Taras-Bilyk/vaz_car/stl_objects/bamper_a.stl

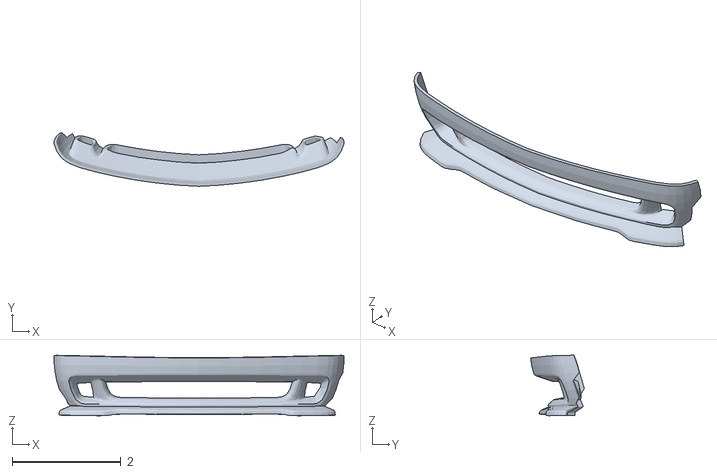
[picture p20: CAD file, 2026-05-01]
stl_objects/bamper_a.stl
5.33 x 0.988 x 1.11
