Taras-Bilyk/vaz_car/stl_objects/splitter_left_bottom.stl

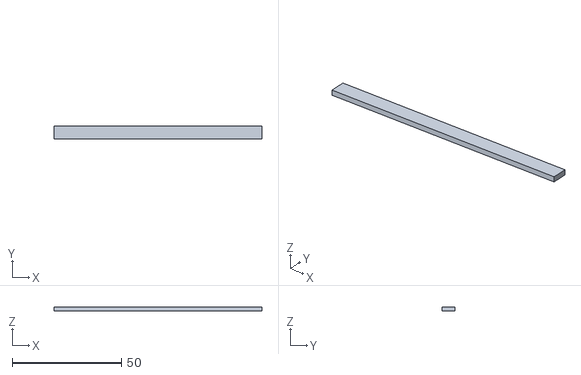
[picture p21: CAD file, 2026-05-01]
stl_objects/splitter_left_bottom.stl
95.0 x 6.00 x 2.00
