Taras-Bilyk/vaz_car/stl_objects/base_bottom.stl

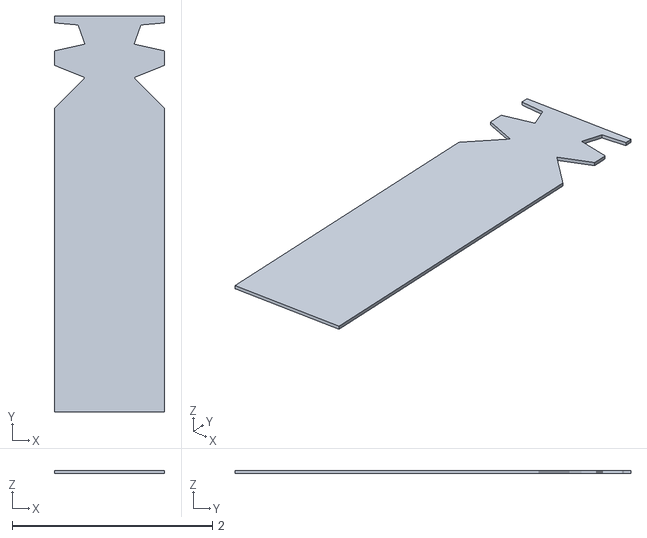
[picture p22: CAD file, 2026-05-01]
stl_objects/base_bottom.stl
1.10 x 3.95 x 0.03
