Taras-Bilyk/vaz_car/stl_objects/kapot.stl

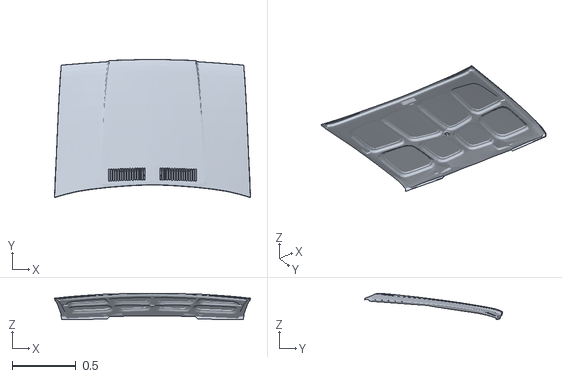
[picture p23: CAD file, 2026-05-01]
stl_objects/kapot.stl
1.54 x 1.09 x 0.208
