Taras-Bilyk/vaz_car/stl_objects/wheel_v2.stl

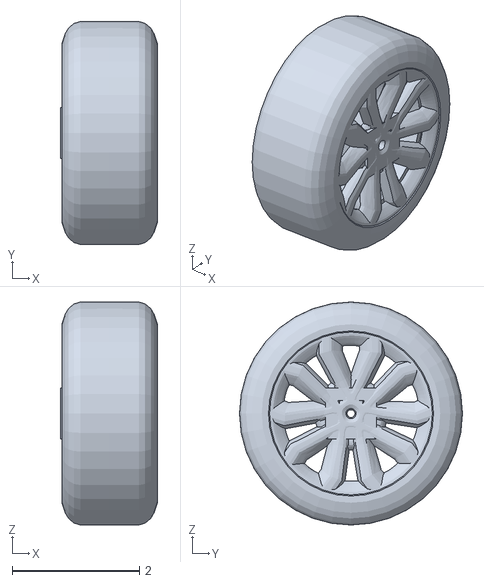
[picture p24: CAD file, 2026-05-01]
stl_objects/wheel_v2.stl
1.52 x 3.50 x 3.50
