Taras-Bilyk/vaz_car/stl_objects/base_body.stl

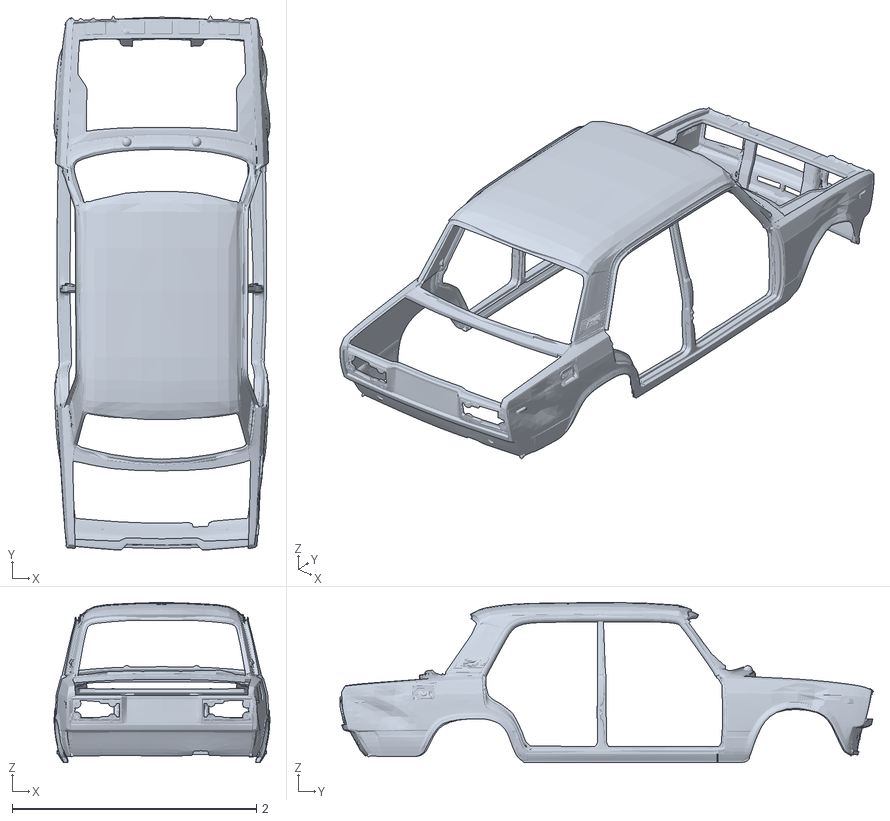
[picture p25: CAD file, 2026-05-01]
stl_objects/base_body.stl
1.77 x 4.38 x 1.31
