Taras-Bilyk/vaz_car/stl_objects/cross_window.stl

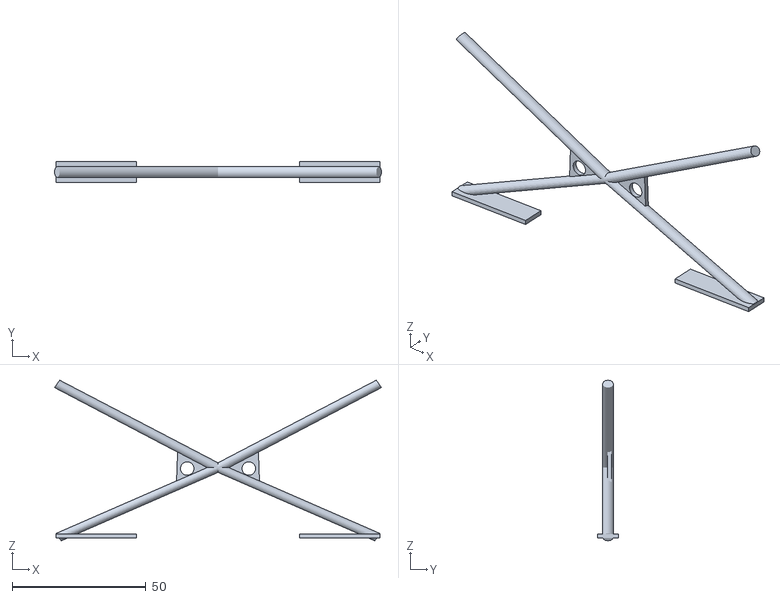
[picture p26: CAD file, 2026-05-01]
stl_objects/cross_window.stl
122.1 x 8.00 x 60.0
