Taras-Bilyk/vaz_car/stl_objects/inc_front.stl

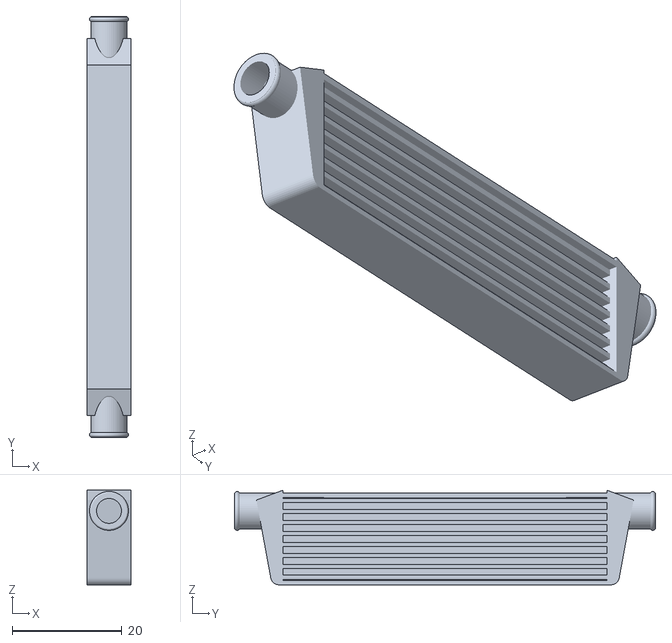
[picture p27: CAD file, 2026-05-01]
stl_objects/inc_front.stl
8.00 x 76.7 x 17.2
